KidsLabDe/nerdYcontroller/kidslab-lamp/schem-images/raspberry-pi-pico.png

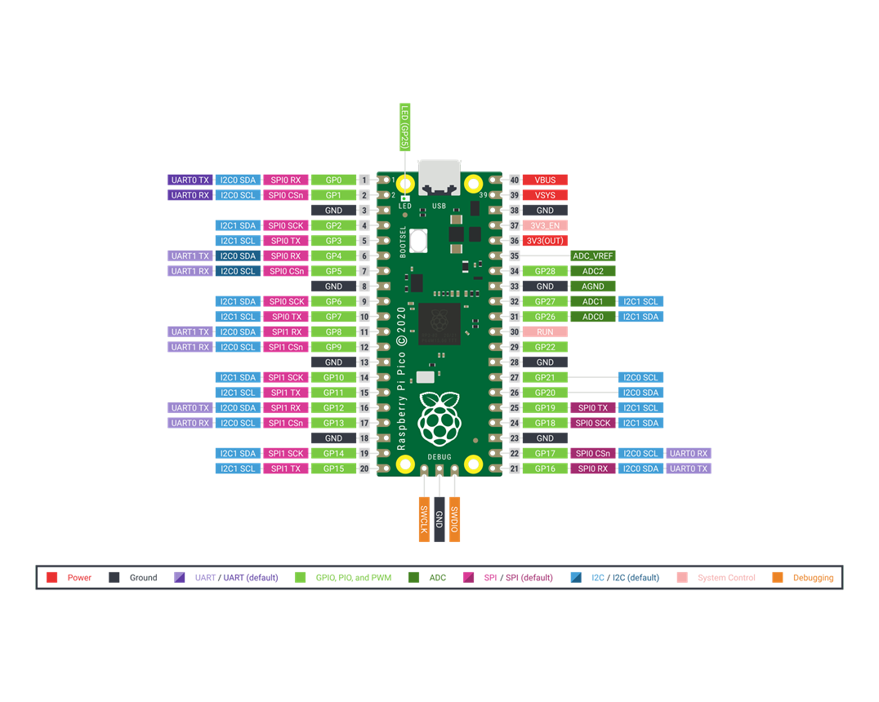
kidslab-lamp/schem-images/raspberry-pi-pico.png
