KidsLabDe/nerdYcontroller/kidslab-lamp_first_screenshot.png

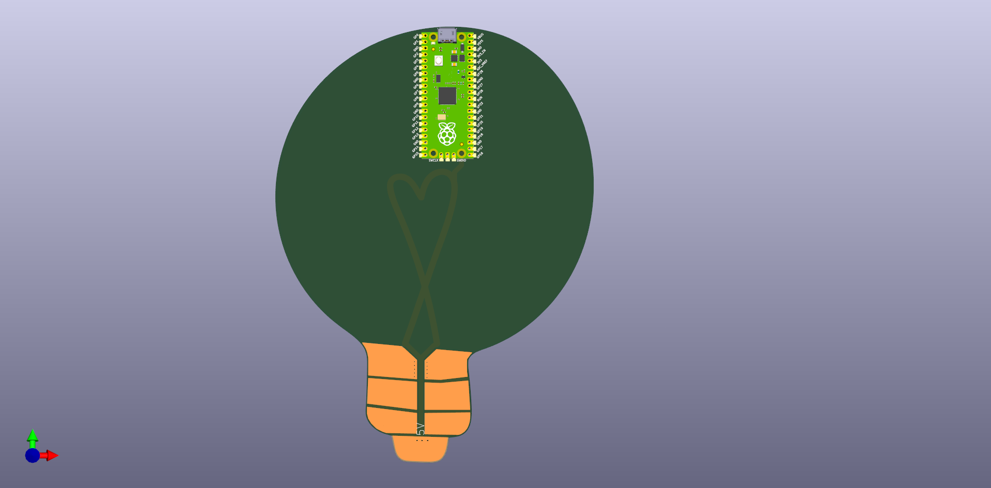
kidslab-lamp_first_screenshot.png
