KidsLabDe/nerdYcontroller/kidslab-lamp_first_screenshot_back.png

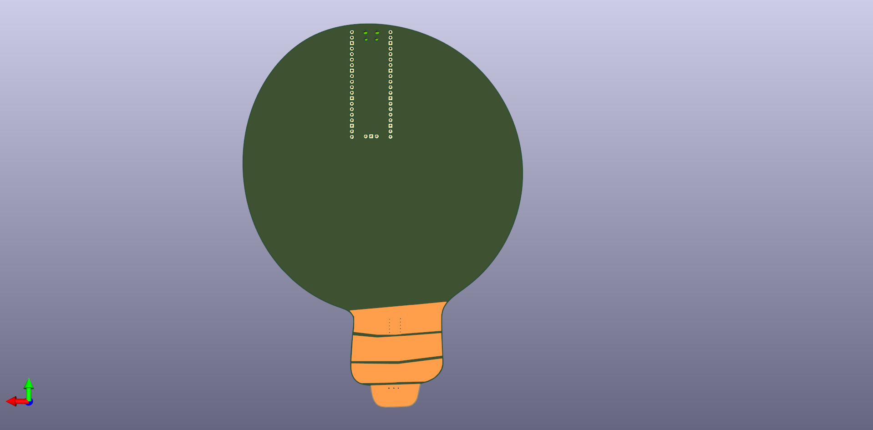
kidslab-lamp_first_screenshot_back.png
