KidsLabDe/nerdYcontroller/kidslab-lamp_second_screenshot.png

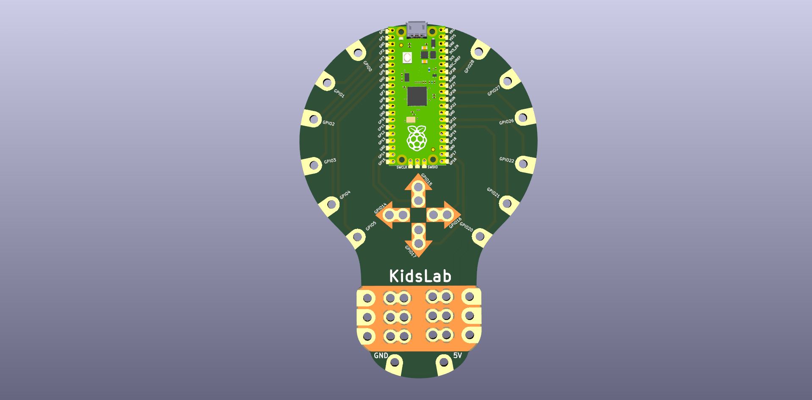
kidslab-lamp_second_screenshot.png
