KidsLabDe/nerdYcontroller/photos/nerdYcontroller_rendering_back.png

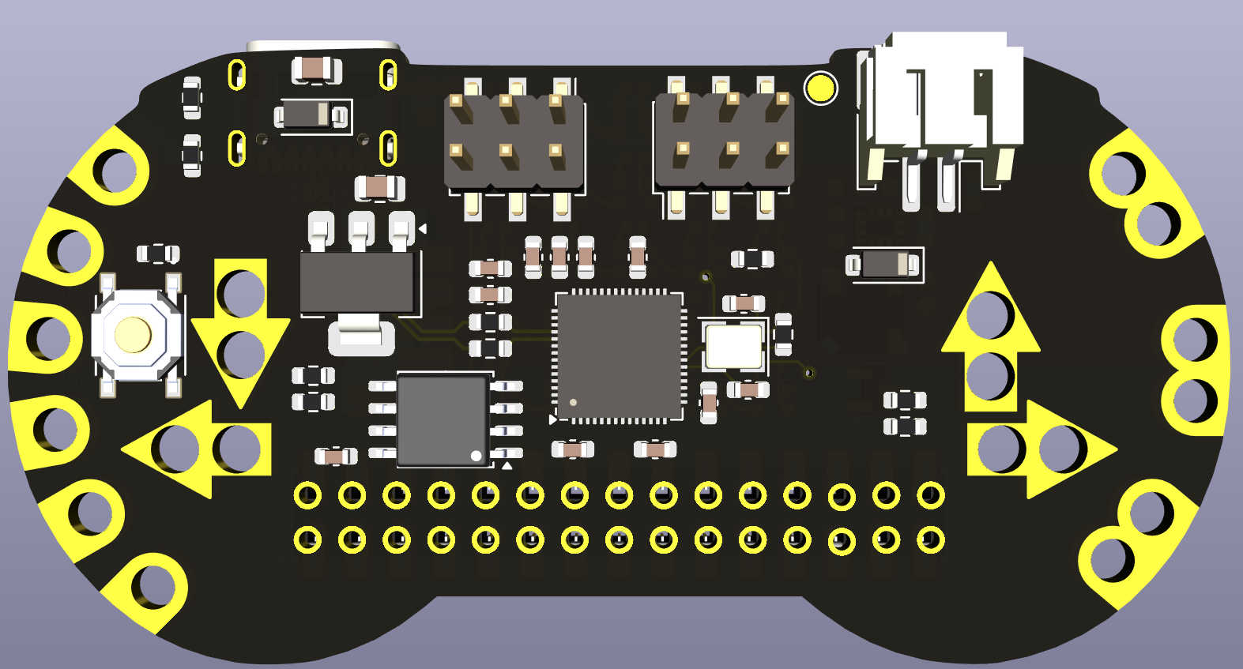
photos/nerdYcontroller_rendering_back.png
