KidsLabDe/nerdYcontroller/photos/nerdYcontroller_rendering_front.png

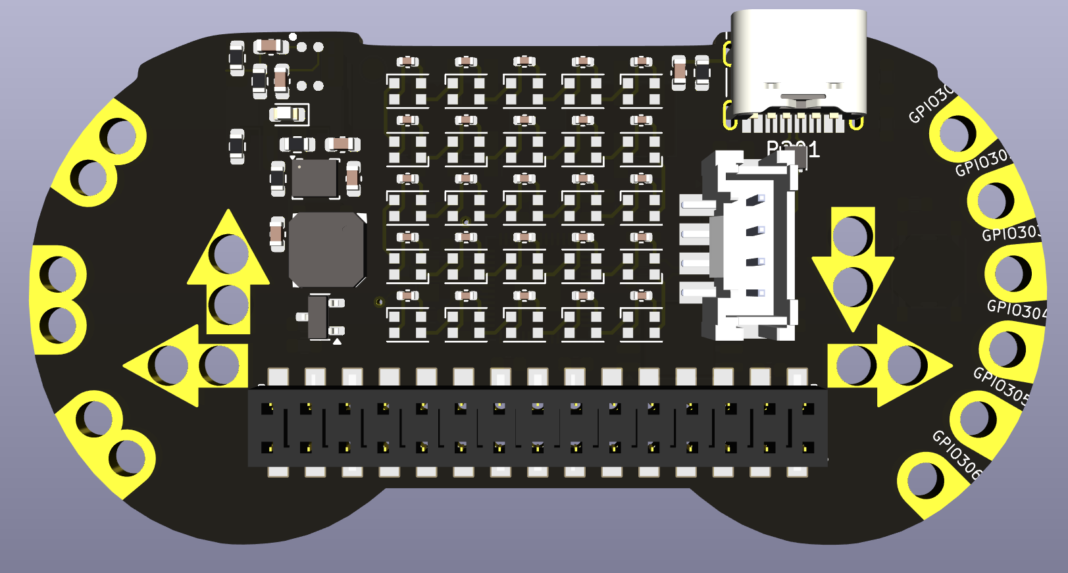
photos/nerdYcontroller_rendering_front.png
